KLPJOA002/BSL-3-Stage-Top-Incubator/Notes/Design Notes/Design 1_260203_165241.pdf

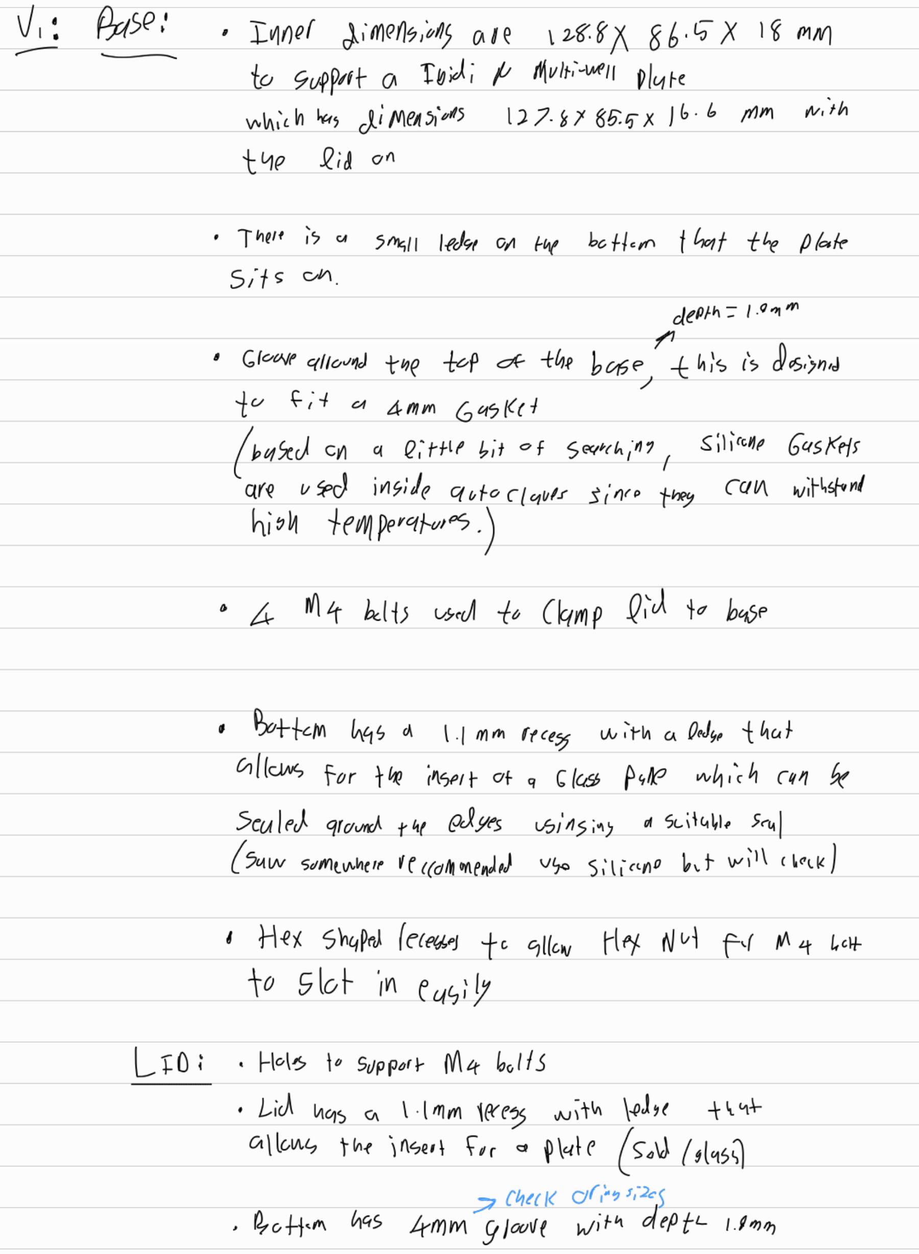
[picture p24: page 1]
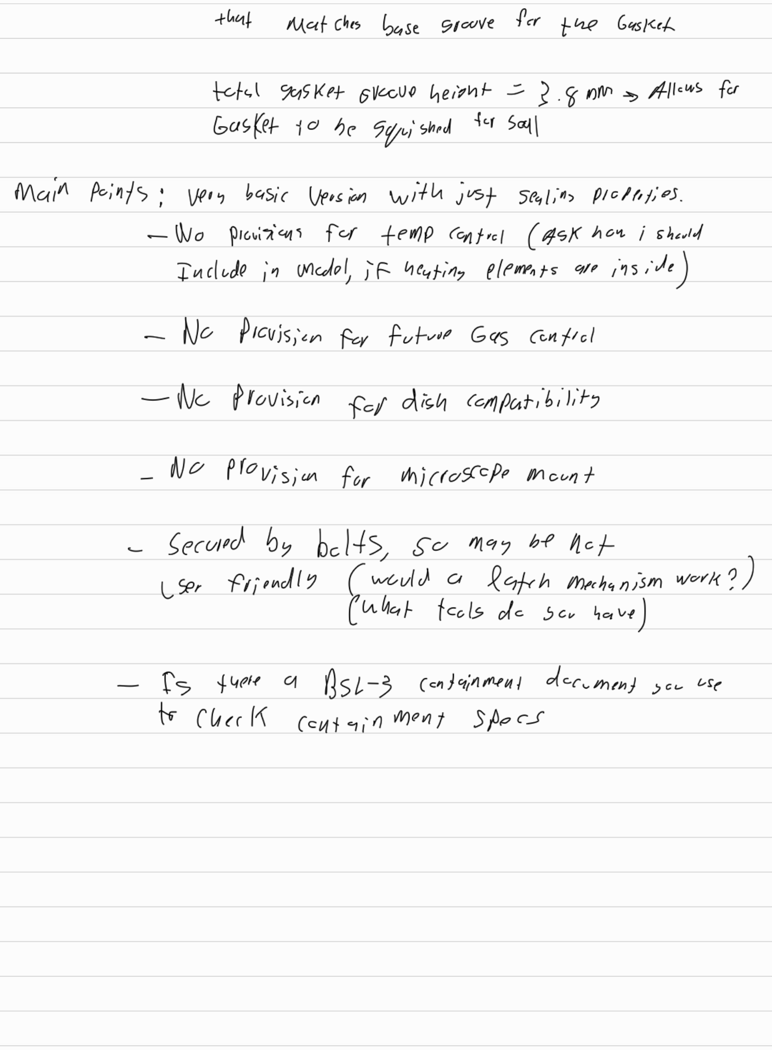
[picture p25: page 2]
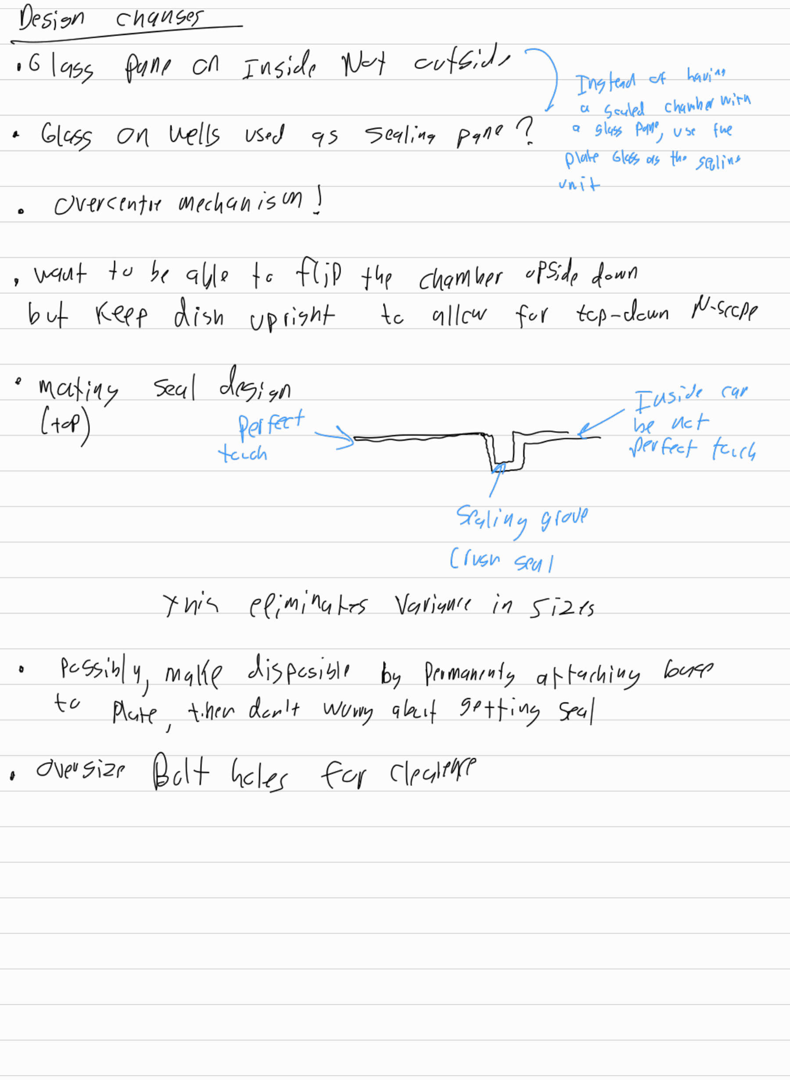
[picture p26: page 3]
