KLPJOA002/BSL-3-Stage-Top-Incubator/Notes/Design Notes/Design 3_260206_163951.pdf

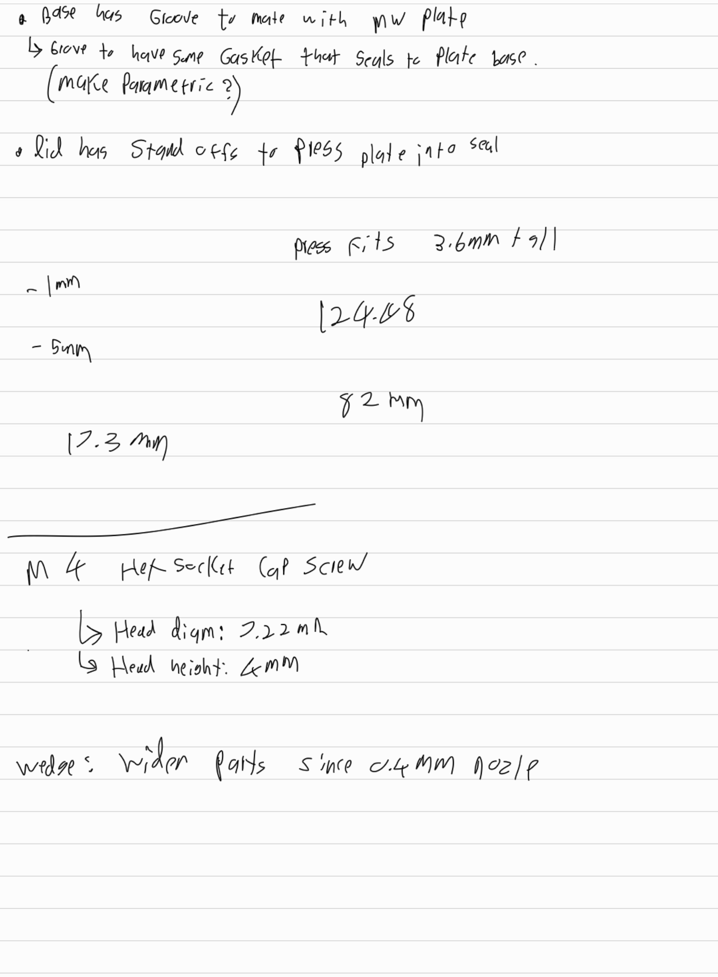
[picture p27: page 1]
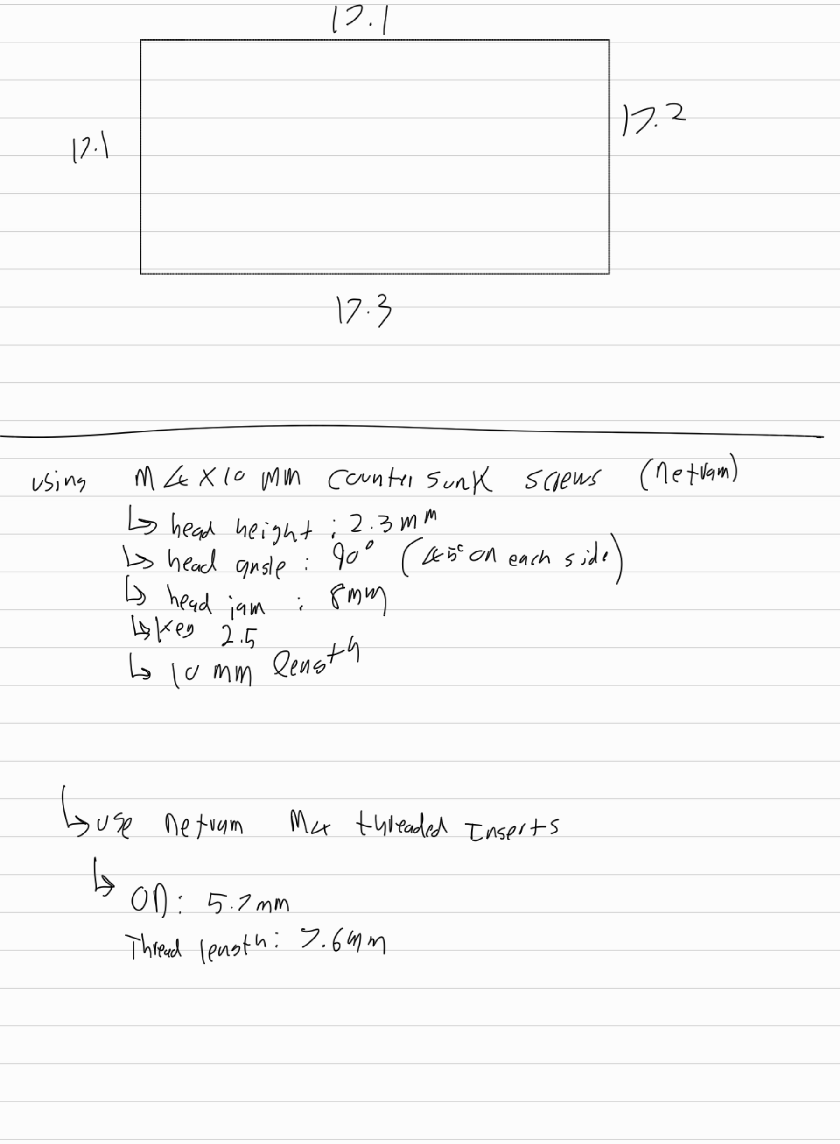
[picture p28: page 2]
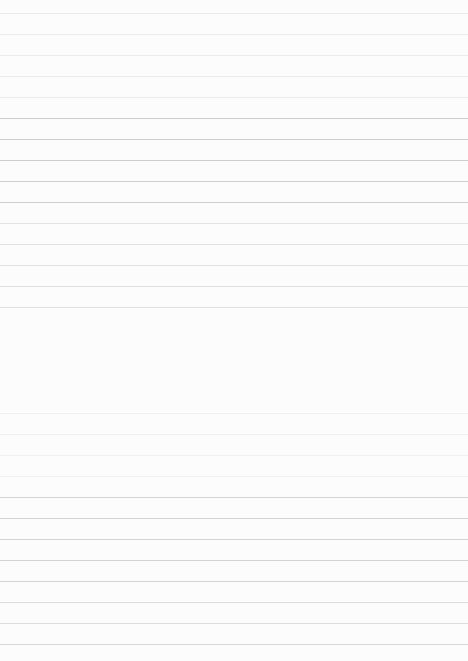
[picture p29: page 3]
