KLPJOA002/BSL-3-Stage-Top-Incubator/Notes/Design Notes/IP Ratings_260127_100130.pdf

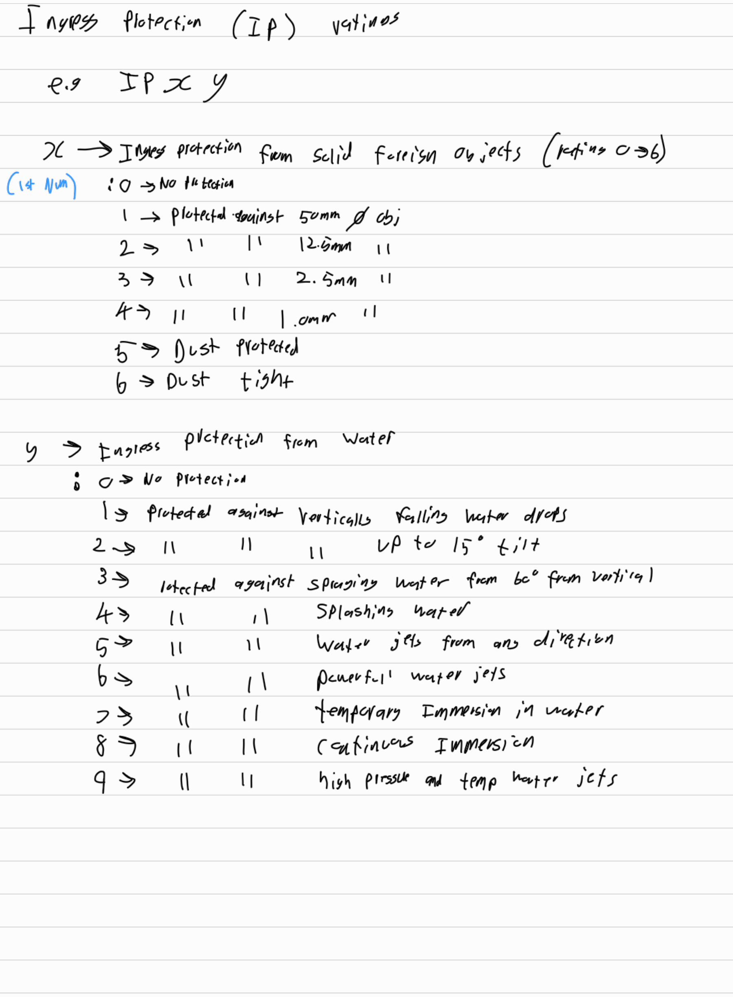
[picture p30: page 1]
