KLPJOA002/BSL-3-Stage-Top-Incubator/Double_Gasket_Rought_Sketch.png

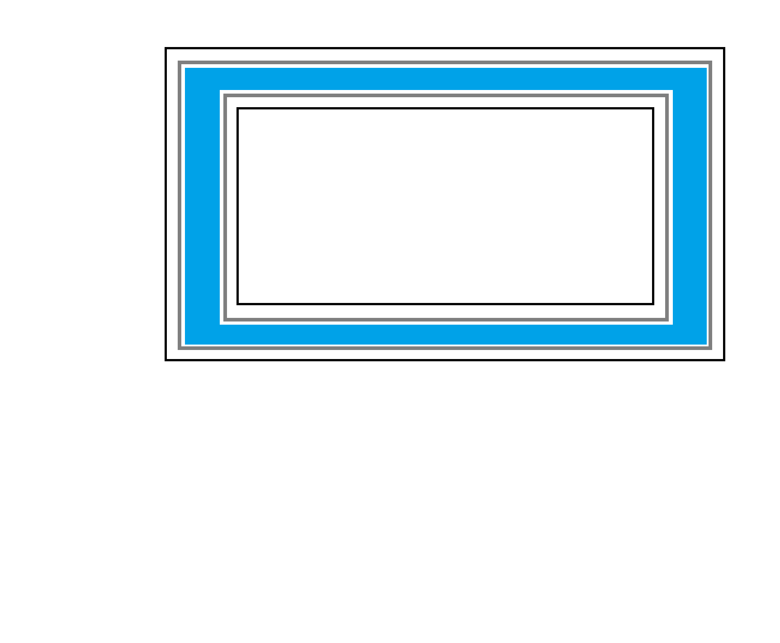
Double_Gasket_Rought_Sketch.png
