KLPJOA002/BSL-3-Stage-Top-Incubator/Research Documents/Existing BSL3 Incubator Logs/20260120_105519.jpg

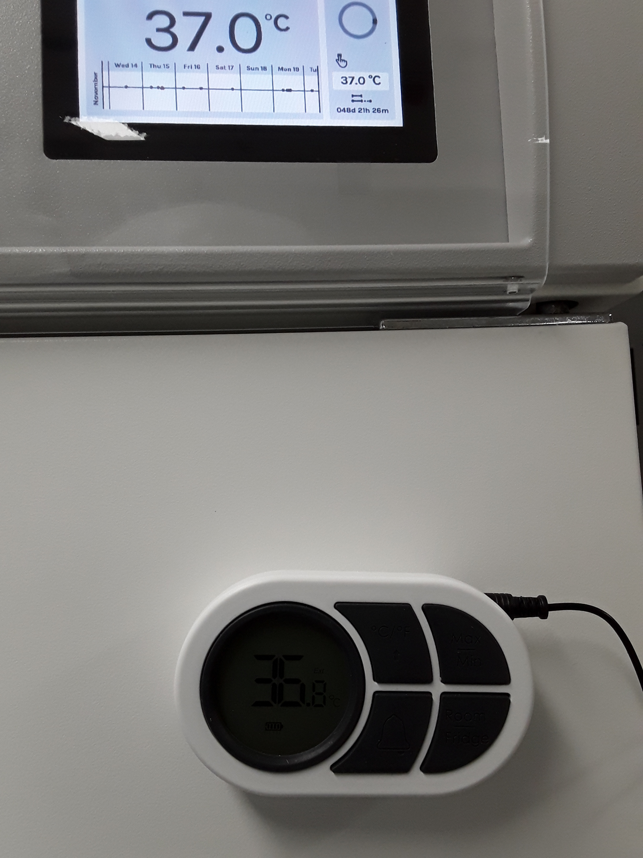
Research Documents/Existing BSL3 Incubator Logs/20260120_105519.jpg
